bobis1/devboard/DevboardArt/Board.excalidraw.png

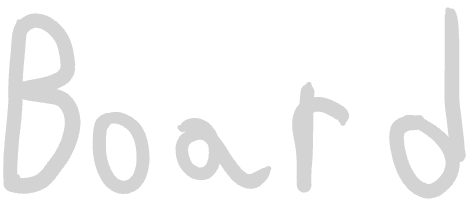
DevboardArt/Board.excalidraw.png
