bobis1/devboard/DevboardArt/Edu.excalidraw.png

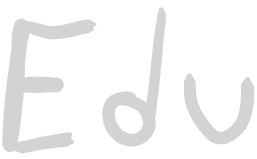
DevboardArt/Edu.excalidraw.png
