bobis1/devboard/DevboardArt/pcb.png

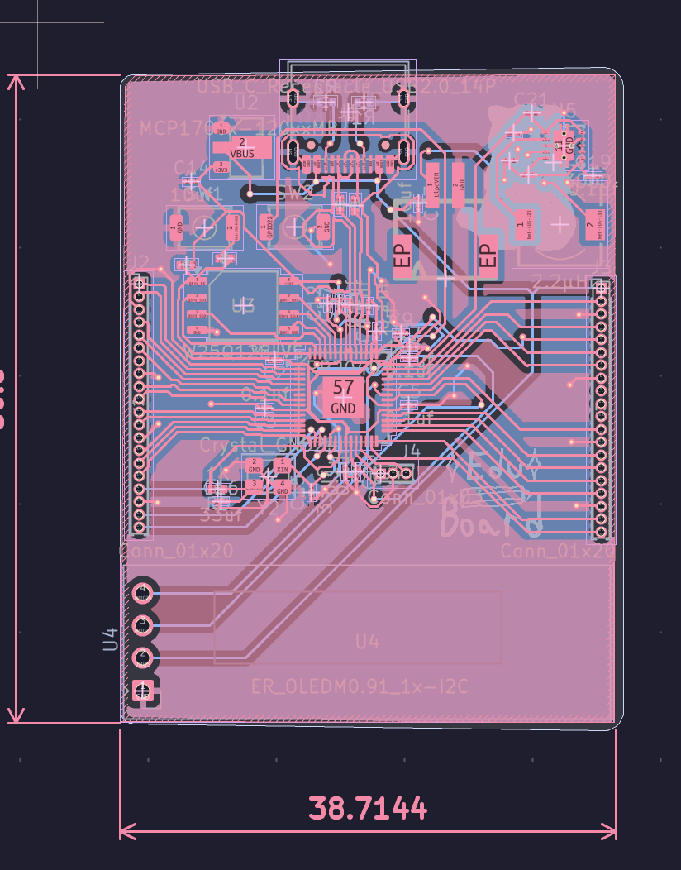
DevboardArt/pcb.png
