bobis1/devboard/DevboardArt/Pencil.excalidraw.png

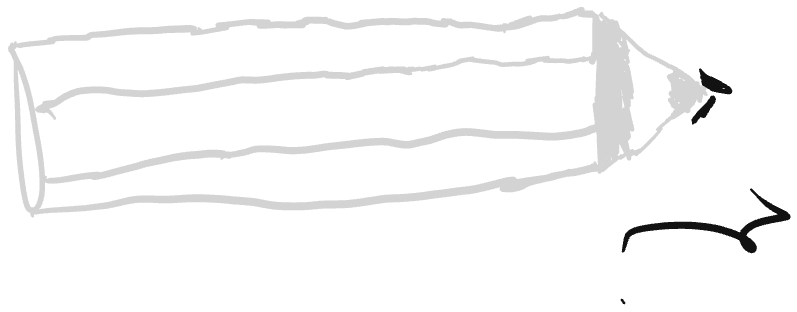
DevboardArt/Pencil.excalidraw.png
