bobis1/devboard/DevboardArt/Pencil.png

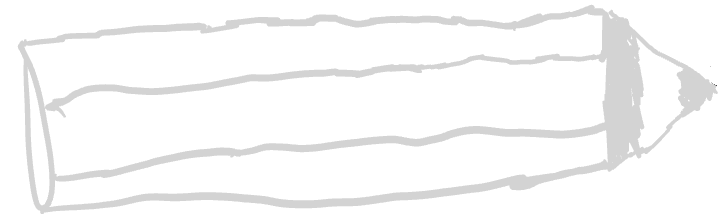
DevboardArt/Pencil.png
