bobis1/devboard/DevboardArt/renders/ExplodedView2.png

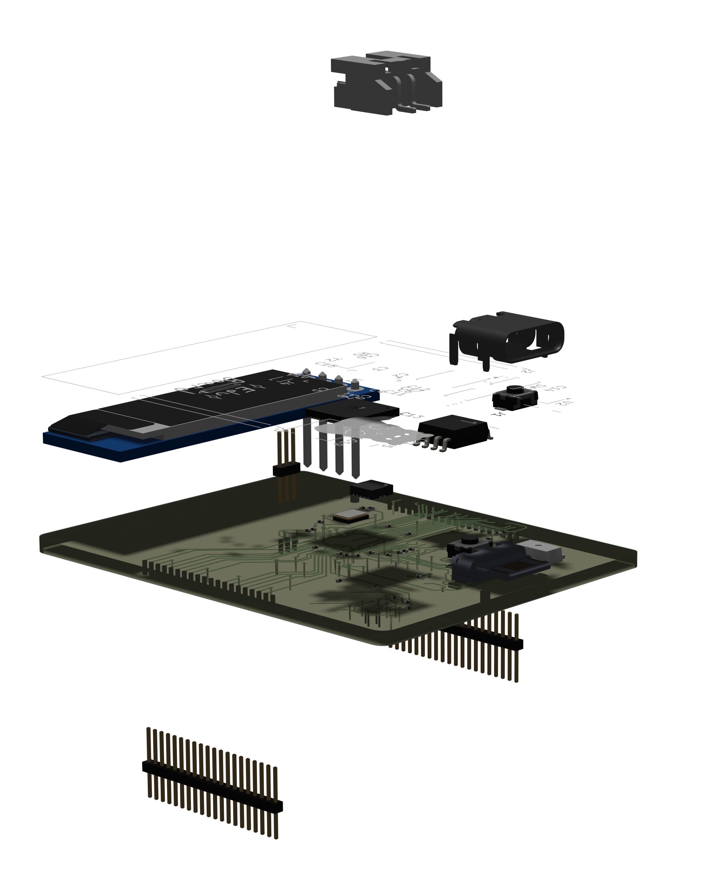
DevboardArt/renders/ExplodedView2.png
