bobis1/devboard/DevboardArt/renders/ExplodedView3.png

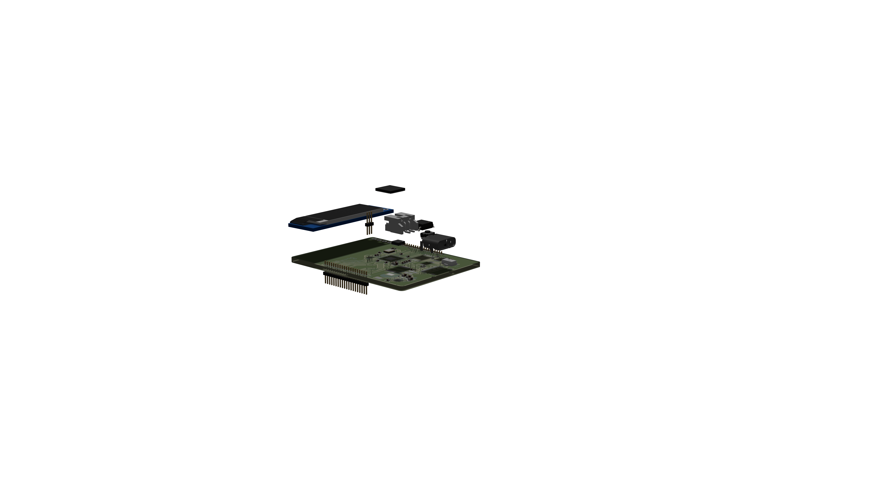
DevboardArt/renders/ExplodedView3.png
