bobis1/devboard/DevboardArt/renders/Component3dmodels/adafruit-jst-ph-2-pin-smt-right-angle-breakout-board-1.snapshot.1/1862-04.jpg

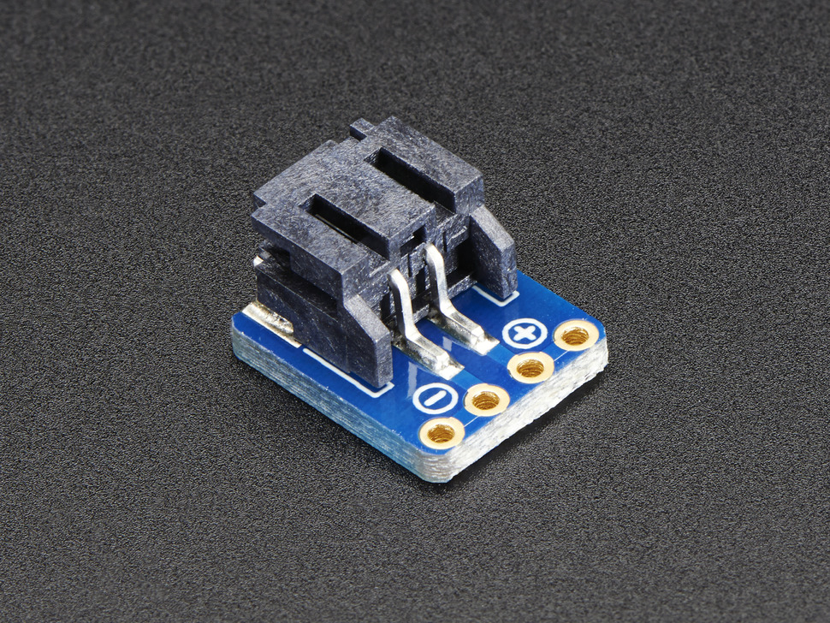
DevboardArt/renders/Component3dmodels/adafruit-jst-ph-2-pin-smt-right-angle-breakout-board-1.snapshot.1/1862-04.jpg
