bobis1/devboard/DevboardArt/renders/Component3dmodels/jst-sh-through-hole-right-angle-connectors-1.snapshot.1/S2B-PH-KL.stp

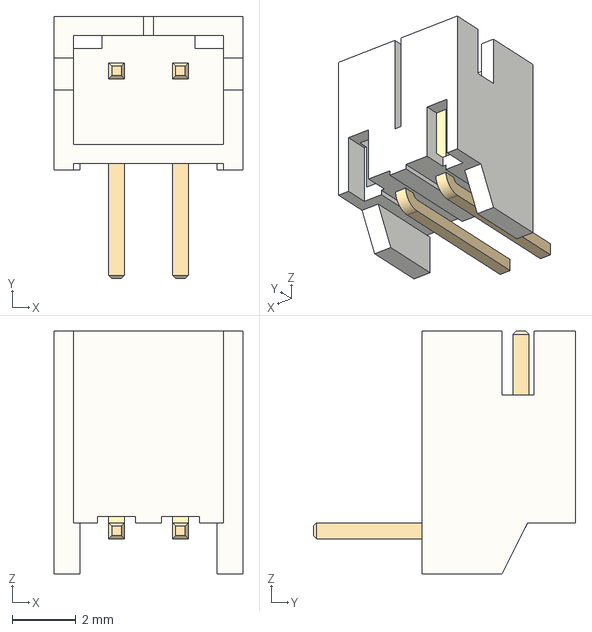
[picture p31: CAD file, 2026-09-02]
DevboardArt/renders/Component3dmodels/jst-sh-through-hole-right-angle-connectors-1.snapshot.1/S2B-PH-KL.stp
5.90 x 8.20 x 7.60 mm
