bobis1/devboard/JournalPictures/Journal5.png

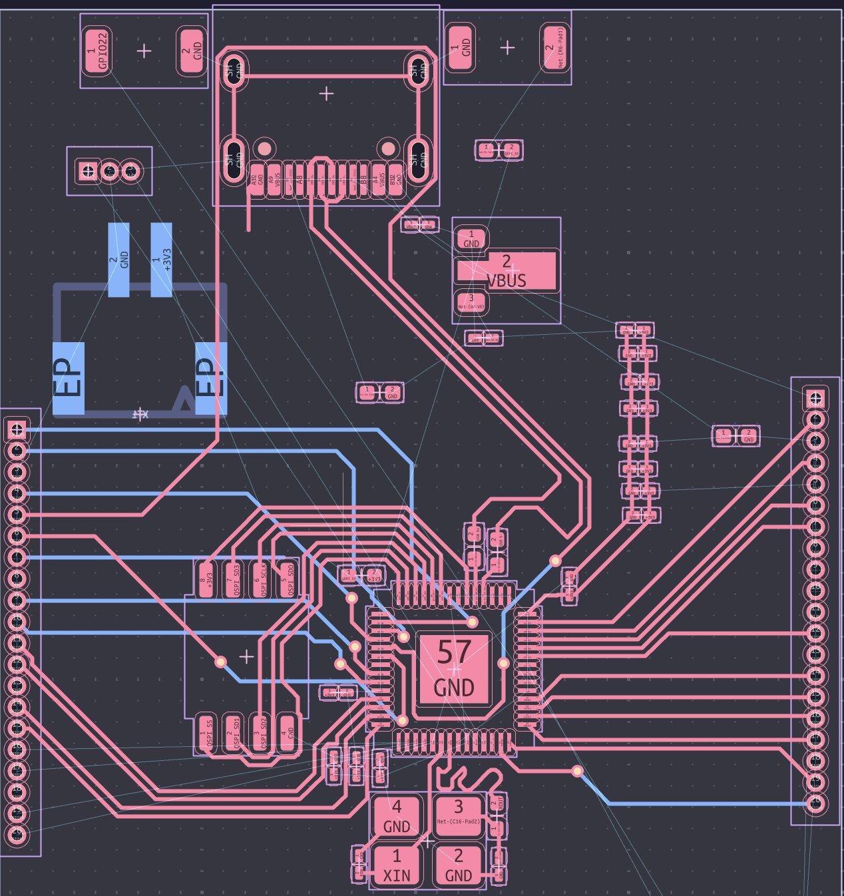
JournalPictures/Journal5.png
