bobis1/devboard/JournalPictures/Screenshot 2026-09-01 at 9.14.24 PM.png

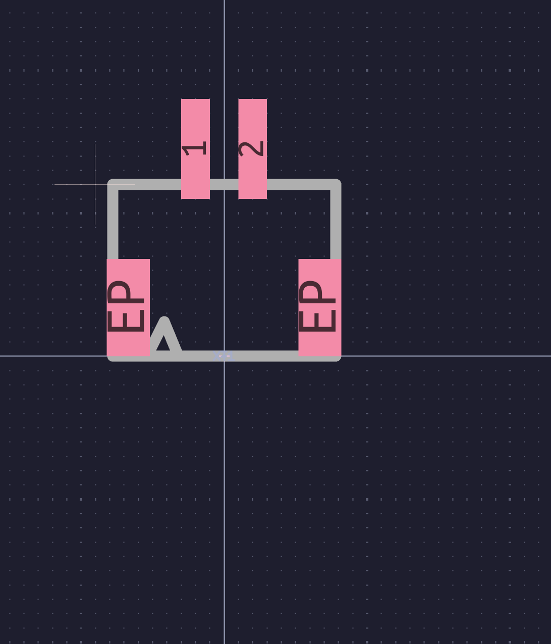
JournalPictures/Screenshot 2026-09-01 at 9.14.24 PM.png
