bobis1/devboard/JournalPictures/Screenshot 2026-09-01 at 9.39.35 PM.png

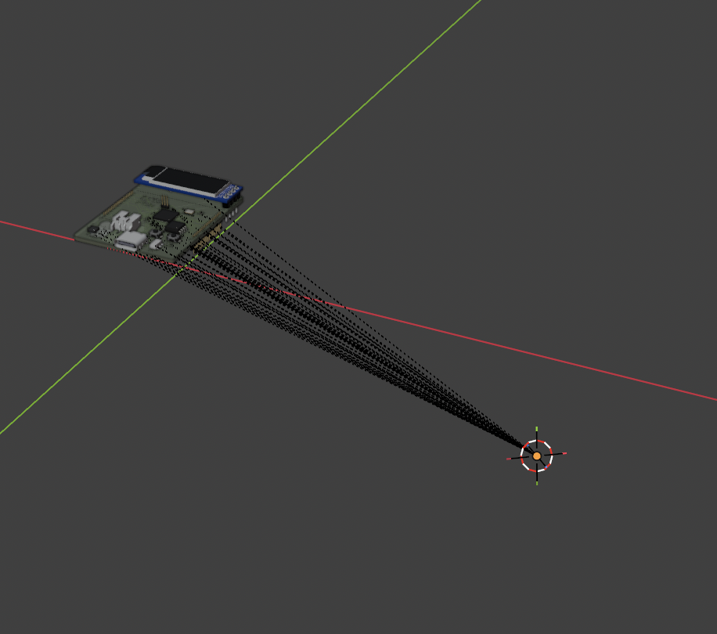
JournalPictures/Screenshot 2026-09-01 at 9.39.35 PM.png
