bobis1/devboard/JournalPictures/Screenshot 2026-09-01 at 9.59.56 PM.png

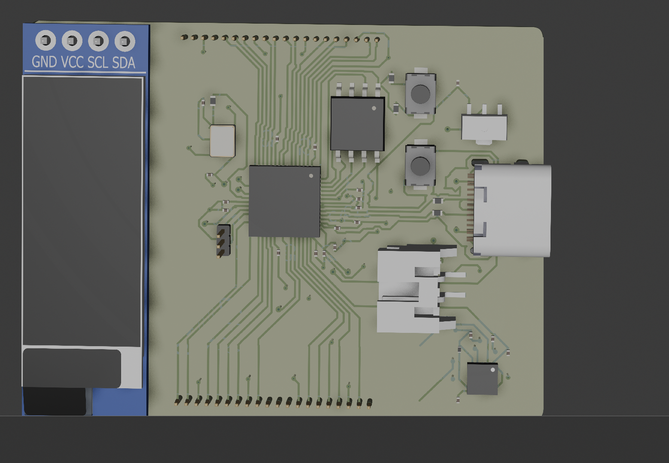
JournalPictures/Screenshot 2026-09-01 at 9.59.56 PM.png
