bobis1/devboard/JournalPictures/Screenshot 2026-09-01 at 10.17.38 PM.png

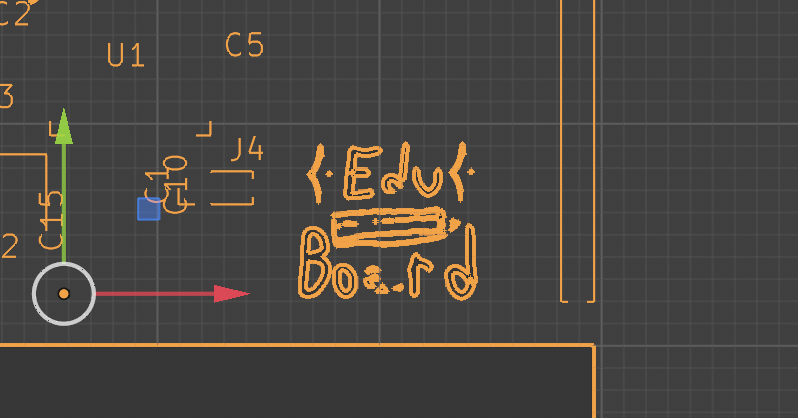
JournalPictures/Screenshot 2026-09-01 at 10.17.38 PM.png
